Mistress-Lukutar/Strat-League-2025/DOC/Flyer/1.jpg

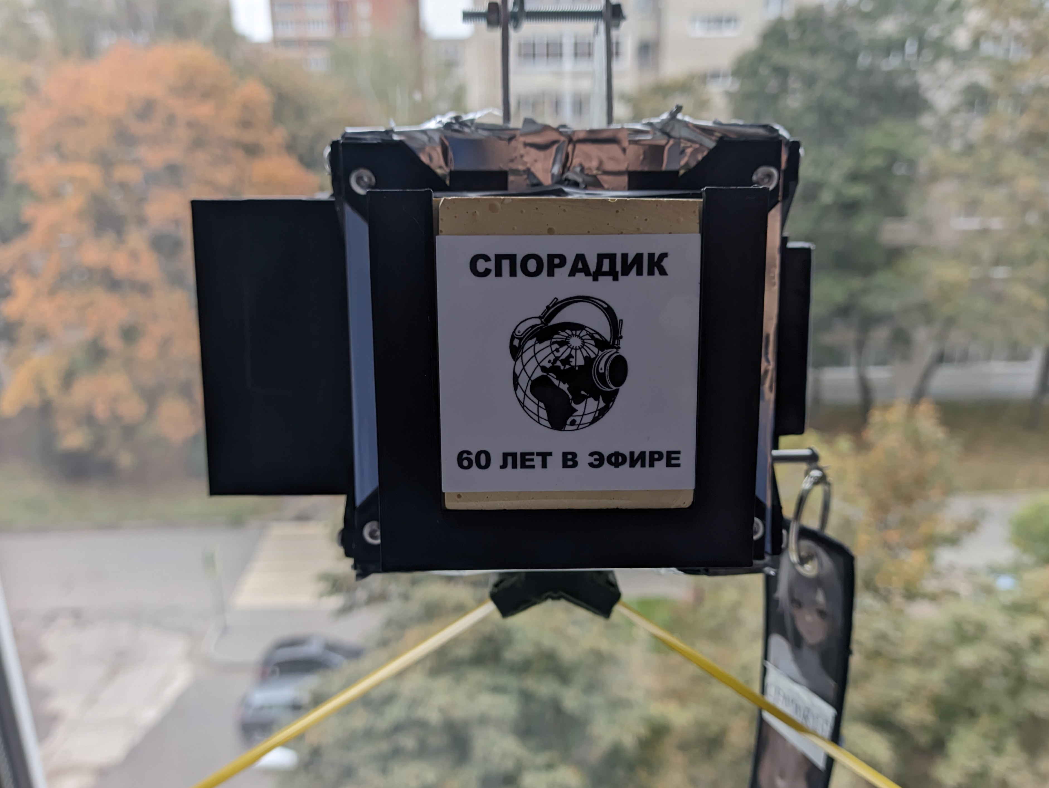
DOC/Flyer/1.jpg
