Mistress-Lukutar/Strat-League-2025/DOC/Flyer/2.jpg

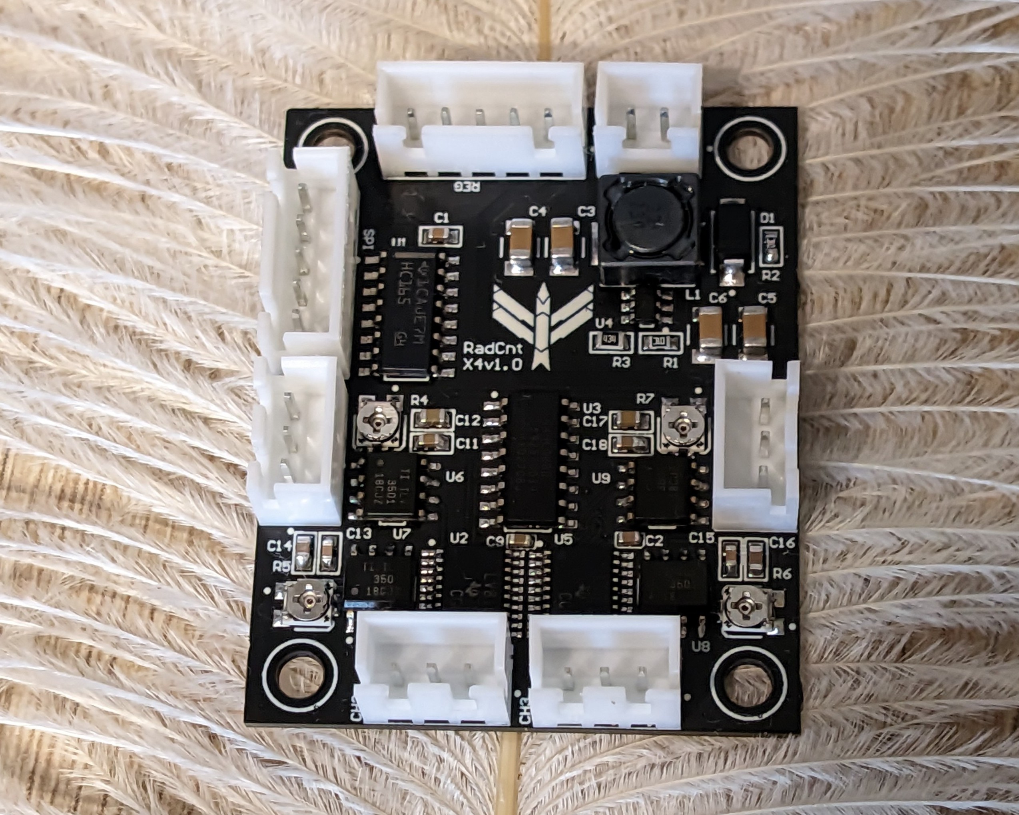
DOC/Flyer/2.jpg
