Mistress-Lukutar/Strat-League-2025/DOC/Flyer/3.jpg

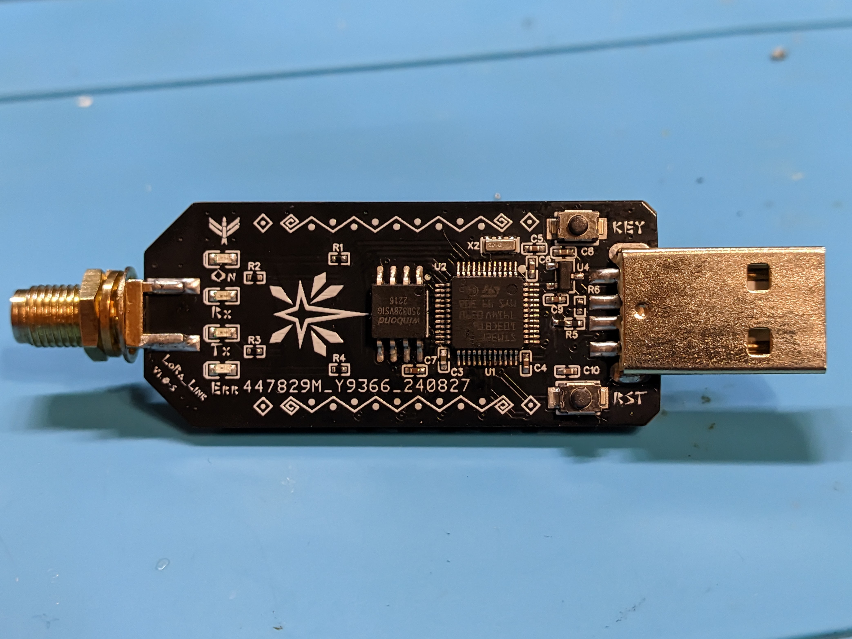
DOC/Flyer/3.jpg
