Mistress-Lukutar/Strat-League-2025/Photos/CubeSat/1.jpg

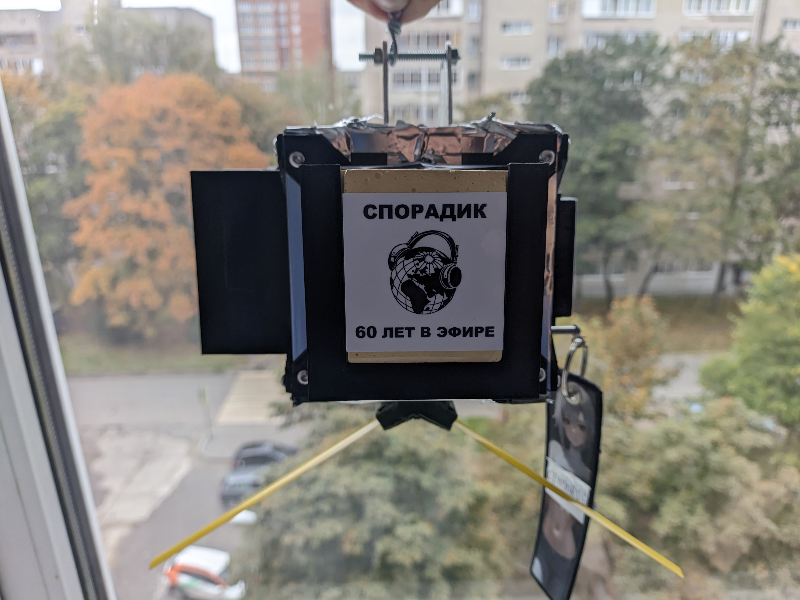
Photos/CubeSat/1.jpg
