Mistress-Lukutar/Strat-League-2025/Photos/CubeSat/PXL_20250920_075320431.jpg

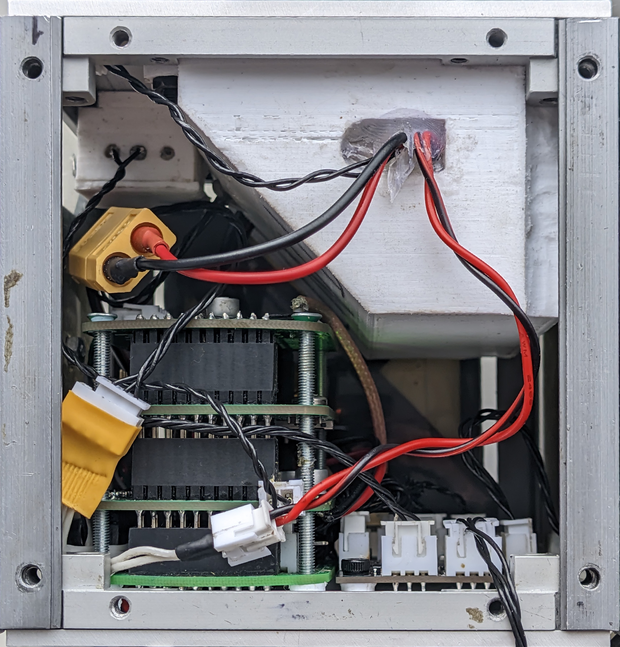
Photos/CubeSat/PXL_20250920_075320431.jpg
