Mistress-Lukutar/Strat-League-2025/Photos/CubeSat/PXL_20250921_090402078.jpg

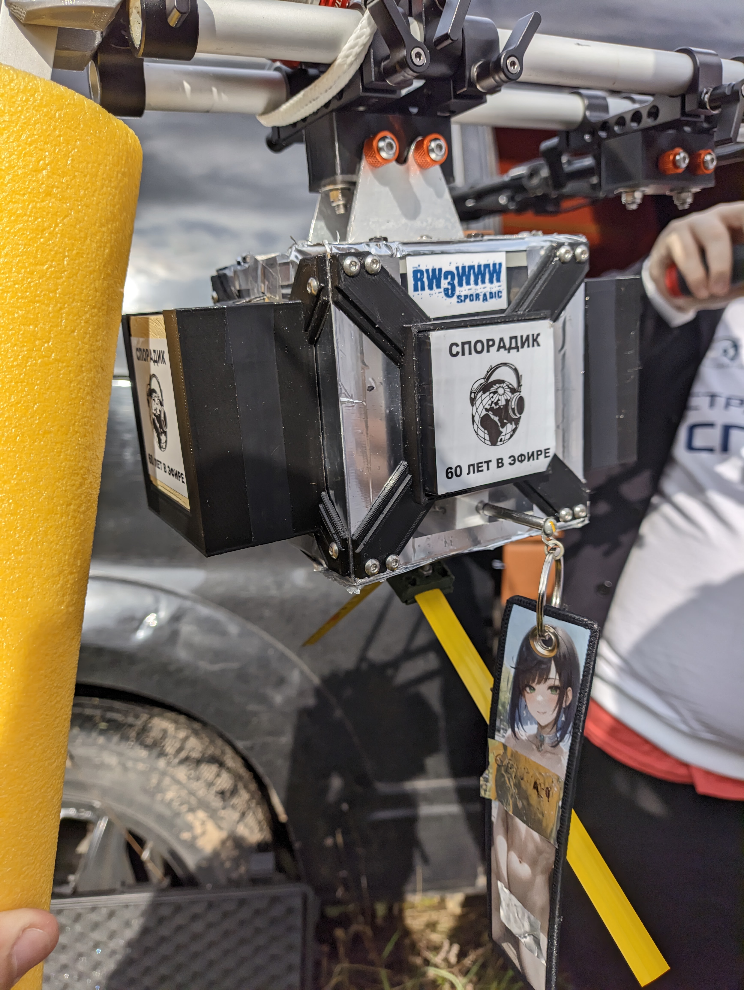
Photos/CubeSat/PXL_20250921_090402078.jpg
