Mistress-Lukutar/Strat-League-2025/Photos/CubeSat/PXL_20250921_094914945.jpg

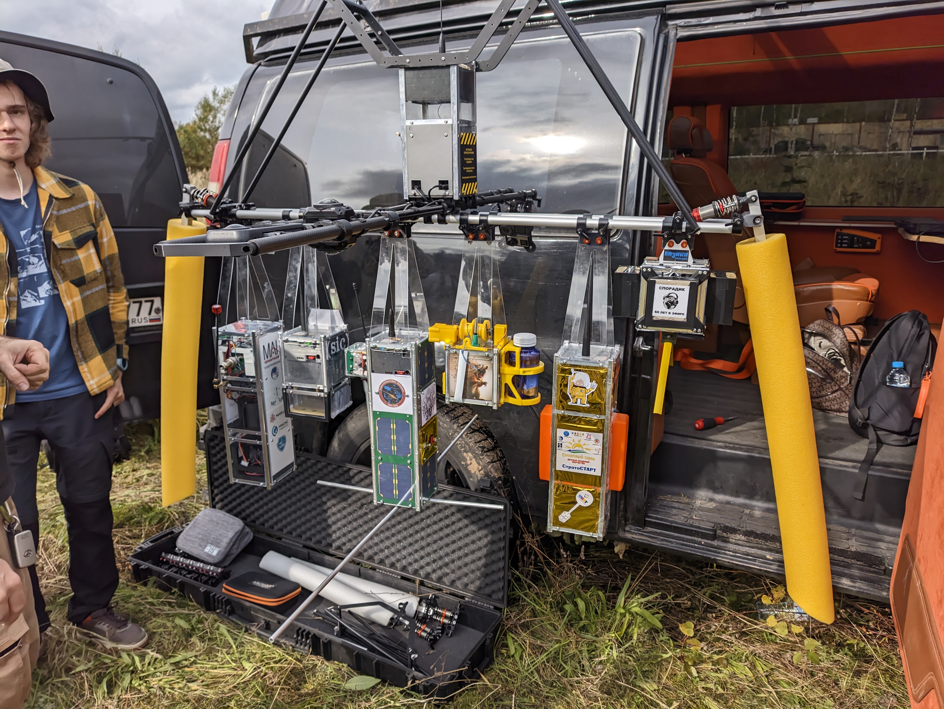
Photos/CubeSat/PXL_20250921_094914945.jpg
