Mistress-Lukutar/Strat-League-2025/Photos/PCB/MCU.jpg

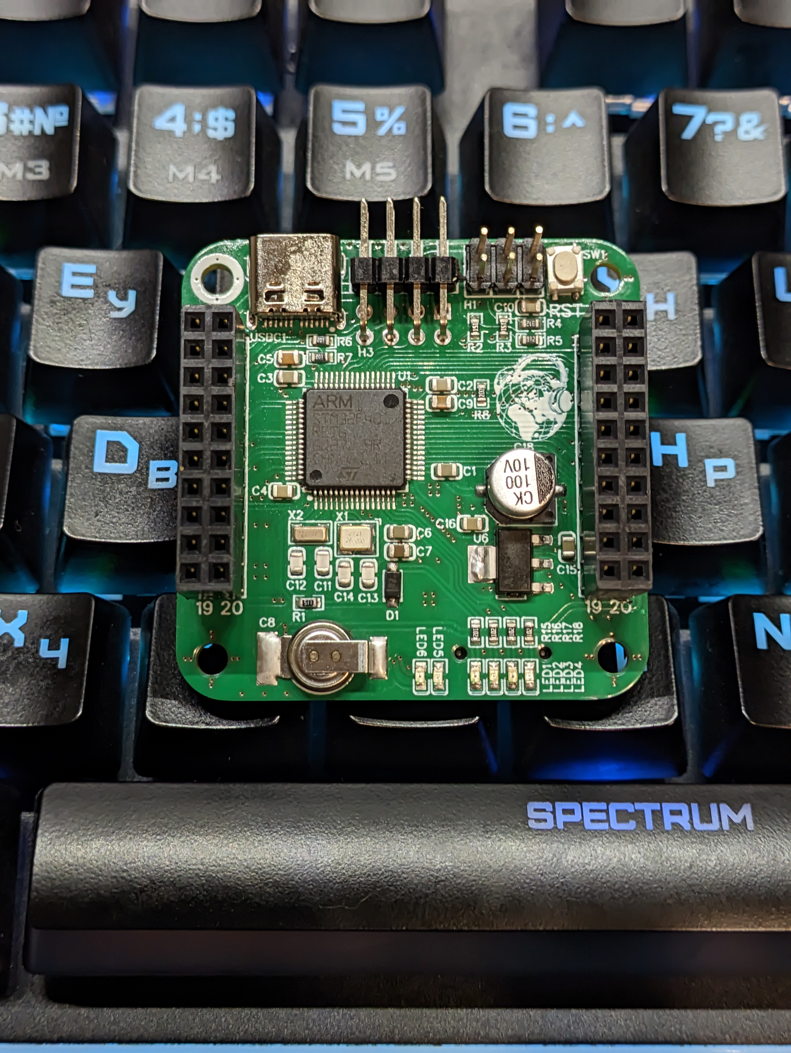
Photos/PCB/MCU.jpg
