Mistress-Lukutar/Strat-League-2025/Photos/plots/03_gyro_4subplots.png

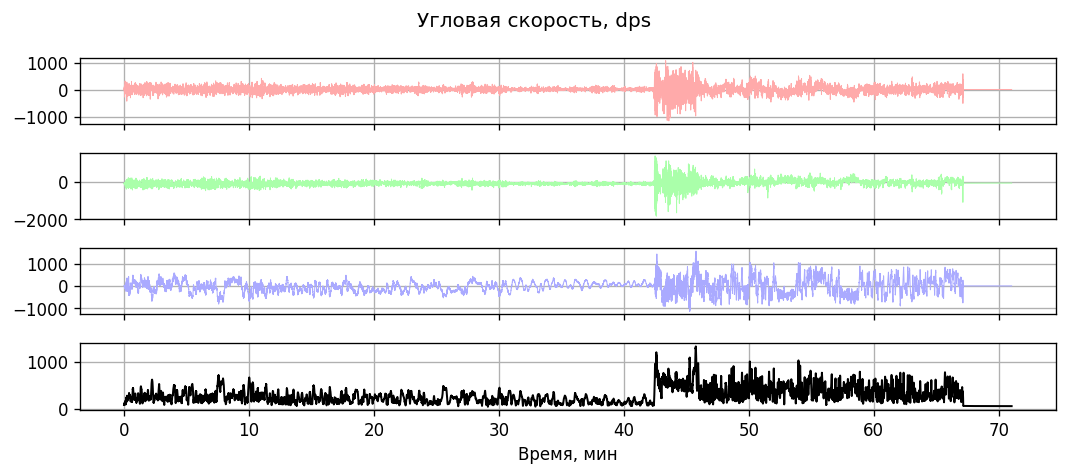
Photos/plots/03_gyro_4subplots.png
