Mistress-Lukutar/Strat-League-2025/Photos/plots/04_rad_sum_four_subplots.png

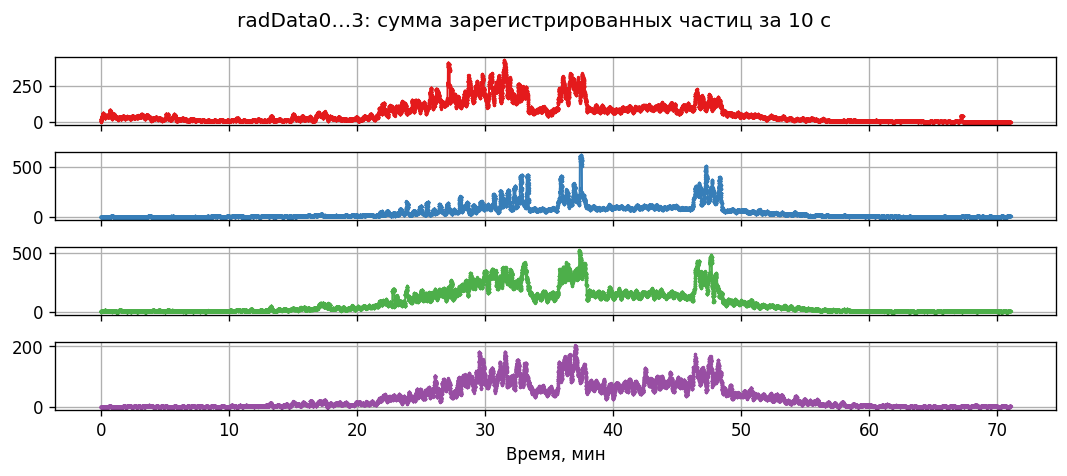
Photos/plots/04_rad_sum_four_subplots.png
